mp-se/kegmon/raw/run1/screen.png

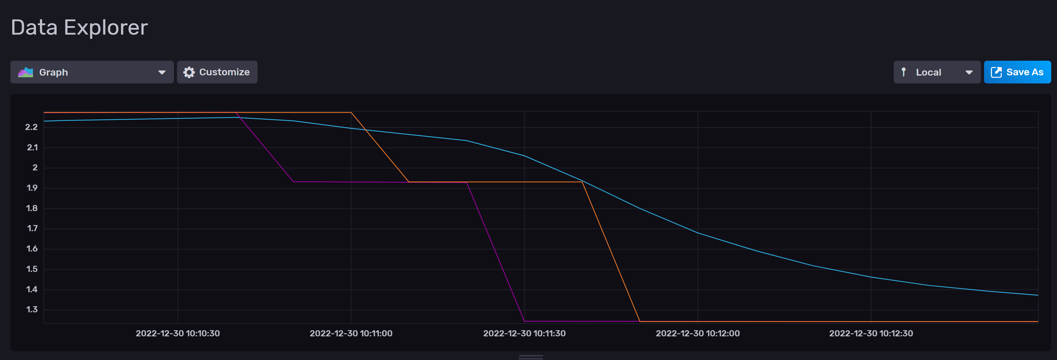
raw/run1/screen.png
