mp-se/kegmon/src_docs/source/images/view_other_about.png

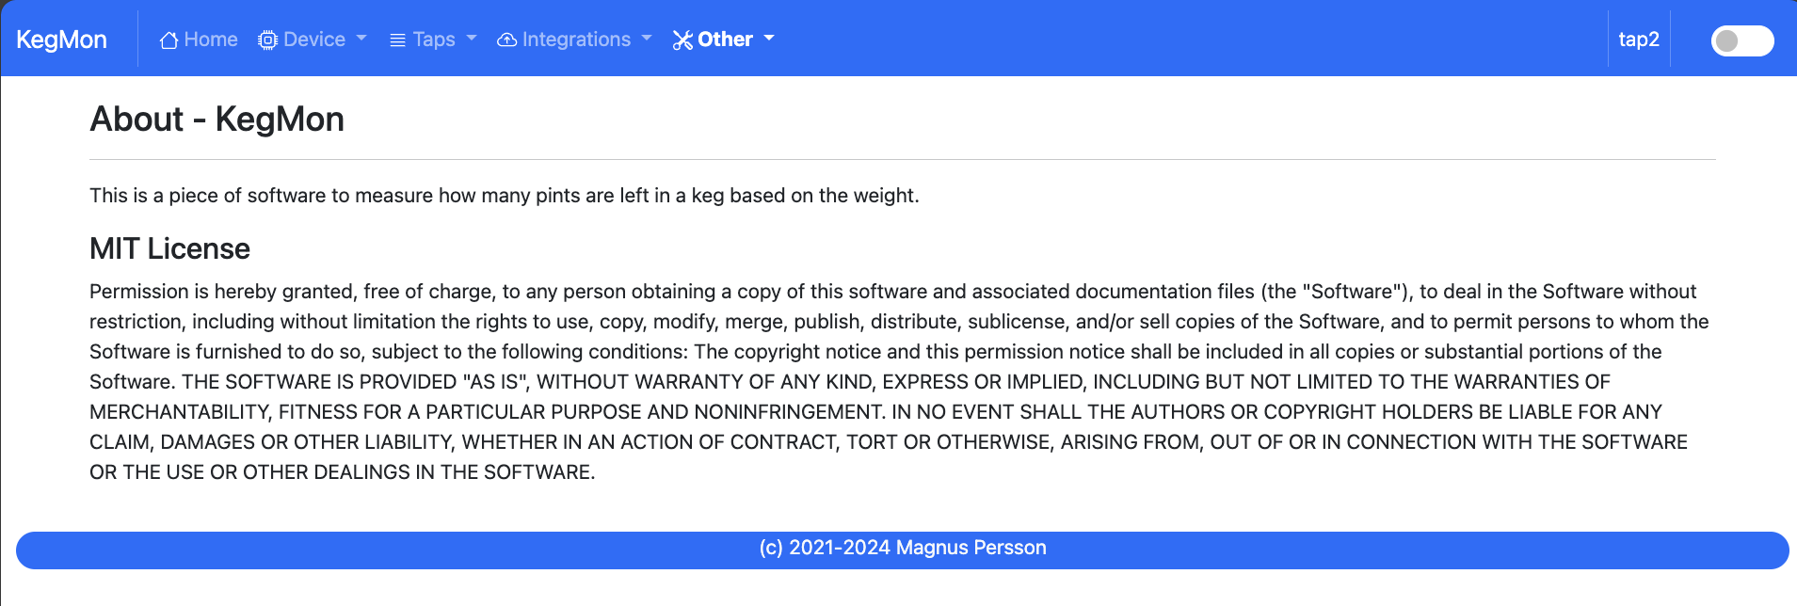
src_docs/source/images/view_other_about.png
