mp-se/kegmon/src/kegconfig.cpp

/*
MIT License

Copyright (c) 2021-2024 Magnus

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
THE SOFTWARE IS PROVIDED "AS IS", WITHOUT WARRANTY OF ANY KIND, EXPRESS OR
IMPLIED, INCLUDING BUT NOT LIMITED TO THE WARRANTIES OF MERCHANTABILITY,
FITNESS FOR A PARTICULAR PURPOSE AND NONINFRINGEMENT. IN NO EVENT SHALL THE
AUTHORS OR COPYRIGHT HOLDERS BE LIABLE FOR ANY CLAIM, DAMAGES OR OTHER
LIABILITY, WHETHER IN AN ACTION OF CONTRACT, TORT OR OTHERWISE, ARISING FROM,
OUT OF OR IN CONNECTION WITH THE SOFTWARE OR THE USE OR OTHER DEALINGS IN THE
SOFTWARE.
 */
#include <kegconfig.hpp>
#include <log.hpp>
#include <main.hpp>
#include <utils.hpp>

constexpr auto PARAM_PLATFORM = "platform";

KegConfig::KegConfig(String baseMDNS, String fileName)
    : BaseConfig(baseMDNS, fileName) {}

void KegConfig::createJson(JsonObject& doc) const {
  // Call base class functions
  createJsonBase(doc);
  createJsonWifi(doc);
  createJsonOta(doc);
  createJsonPush(doc);

  // Handle project specific config
  doc[PARAM_WEIGHT_UNIT] = getWeightUnit();
  doc[PARAM_VOLUME_UNIT] = getVolumeUnit();

  doc[PARAM_DISPLAY_LAYOUT] = getDisplayLayoutTypeAsInt();
  doc[PARAM_TEMP_SENSOR] = getTempSensorTypeAsInt();
  doc[PARAM_SCALE_SENSOR] = getScaleSensorTypeAsInt();
  doc[PARAM_DISPLAY_DRIVER] = getDisplayDriverTypeAsInt();
  // doc[PARAM_LEVEL_DETECTION] = getLevelDetectionAsInt();

  doc[PARAM_BREWFATHER_APIKEY] = getBrewfatherApiKey();
  doc[PARAM_BREWFATHER_USERKEY] = getBrewfatherUserKey();

  doc[PARAM_BREWPI_URL] = getBrewpiUrl();
  doc[PARAM_CHAMBERCTRL_URL] = getChamberCtrlUrl();

  doc[PARAM_BREWLOGGER_URL] = getBrewLoggerUrl();

  doc[PARAM_BREWSPY_TOKEN1] = getBrewspyToken(UnitIndex::U1);
  doc[PARAM_BREWSPY_TOKEN2] = getBrewspyToken(UnitIndex::U2);

  doc[PARAM_BARHELPER_APIKEY] = getBarhelperApiKey();
  doc[PARAM_BARHELPER_MONITOR1] = getBarhelperMonitor(UnitIndex::U1);
  doc[PARAM_BARHELPER_MONITOR2] = getBarhelperMonitor(UnitIndex::U2);

  doc[PARAM_SCALE_TEMP_FORMULA1] =
      getScaleTempCompensationFormula(UnitIndex::U1);
  doc[PARAM_SCALE_FACTOR1] =
      serialized(String(getScaleFactor(UnitIndex::U1), 5));
  doc[PARAM_SCALE_OFFSET1] = getScaleOffset(UnitIndex::U1);
  doc[PARAM_KEG_WEIGHT1] =
      serialized(String(convertOutgoingWeight(getKegWeight(UnitIndex::U1)),
                        getWeightPrecision()));
  doc[PARAM_KEG_VOLUME1] = serialized(String(
      getKegVolume(UnitIndex::U1),
      getWeightPrecision()));  // Dont convert this part (drop down in UI)
  doc[PARAM_GLASS_VOLUME1] = serialized(String(
      getGlassVolume(UnitIndex::U1),
      getWeightPrecision()));  // Dont convert this part (drop down in UI)
  doc[PARAM_BEER_NAME1] = getBeerName(UnitIndex::U1);
  doc[PARAM_BEER_ID1] = getBeerId(UnitIndex::U1);
  doc[PARAM_BEER_ABV1] = serialized(String(getBeerABV(UnitIndex::U1), 2));
  doc[PARAM_BEER_FG1] = serialized(String(getBeerFG(UnitIndex::U1), 2));
  doc[PARAM_BEER_EBC1] = getBeerEBC(UnitIndex::U1);
  doc[PARAM_BEER_IBU1] = getBeerIBU(UnitIndex::U1);

  doc[PARAM_SCALE_TEMP_FORMULA2] =
      getScaleTempCompensationFormula(UnitIndex::U2);
  doc[PARAM_SCALE_FACTOR2] =
      serialized(String(getScaleFactor(UnitIndex::U2), 5));
  doc[PARAM_SCALE_OFFSET2] = getScaleOffset(UnitIndex::U2);
  doc[PARAM_KEG_WEIGHT2] =
      serialized(String(convertOutgoingWeight(getKegWeight(UnitIndex::U2)),
                        getWeightPrecision()));
  doc[PARAM_KEG_VOLUME2] = serialized(String(
      getKegVolume(UnitIndex::U2),
      getWeightPrecision()));  // Dont convert this part (drop down in UI)
  doc[PARAM_GLASS_VOLUME2] =
      serialized(String(getGlassVolume(UnitIndex::U2),
                        2));  // Dont convert this part (drop down in UI)
  doc[PARAM_BEER_NAME2] = getBeerName(UnitIndex::U2);
  doc[PARAM_BEER_ID2] = getBeerId(UnitIndex::U2);
  doc[PARAM_BEER_ABV2] = serialized(String(getBeerABV(UnitIndex::U2), 2));
  doc[PARAM_BEER_FG2] = serialized(String(getBeerFG(UnitIndex::U2), 2));
  doc[PARAM_BEER_EBC2] = getBeerEBC(UnitIndex::U2);
  doc[PARAM_BEER_IBU2] = getBeerIBU(UnitIndex::U2);

  doc[PARAM_SCALE_DEVIATION_INCREASE] =
      serialized(String(getScaleDeviationIncreaseValue(), 2));
  doc[PARAM_SCALE_DEVIATION_DECREASE] =
      serialized(String(getScaleDeviationDecreaseValue(), 2));
  doc[PARAM_SCALE_DEVIATION_KALMAN] =
      serialized(String(getScaleKalmanDeviationValue(), 2));
  doc[PARAM_SCALE_READ_COUNT] = getScaleReadCount();
  doc[PARAM_SCALE_READ_COUNT_CALIBRATION] = getScaleReadCountCalibration();
  doc[PARAM_SCALE_STABLE_COUNT] = getScaleStableCount();

  doc[PARAM_PIN_DISPLAY_DATA] = getPinDisplayData();
  doc[PARAM_PIN_DISPLAY_CLOCK] = getPinDisplayClock();
  doc[PARAM_PIN_SCALE1_DATA] = getPinScale1Data();
  doc[PARAM_PIN_SCALE1_CLOCK] = getPinScale1Clock();
  doc[PARAM_PIN_SCALE2_DATA] = getPinScale2Data();
  doc[PARAM_PIN_SCALE2_CLOCK] = getPinScale2Clock();
  doc[PARAM_PIN_TEMP_DATA] = getPinTempData();
  doc[PARAM_PIN_TEMP_POWER] = getPinTempPower();

#if defined(ESP8266)
  doc[PARAM_PLATFORM] = "esp8266";
#elif defined(ESP32S2)
  doc[PARAM_PLATFORM] = "esp32s2";
#elif defined(ESP32S3)
  doc[PARAM_PLATFORM] = "esp32s3";
#else
#error "Unsupported target"
#endif

  /*
  doc[PARAM_KALMAN_ACTIVE] = isKalmanActive();
  doc[PARAM_KALMAN_MEASUREMENT] = getKalmanMeasurement();
  doc[PARAM_KALMAN_ESTIMATION] = getKalmanEstimation();
  doc[PARAM_KALMAN_NOISE] = getKalmanNoise();
  */
}

void KegConfig::parseJson(JsonObject& doc) {
  // Call base class functions
  parseJsonBase(doc);
  parseJsonWifi(doc);
  parseJsonOta(doc);
  parseJsonPush(doc);

  // Handle project specific config
  if (!doc[PARAM_WEIGHT_UNIT].isNull()) setWeightUnit(doc[PARAM_WEIGHT_UNIT]);
  if (!doc[PARAM_VOLUME_UNIT].isNull()) setVolumeUnit(doc[PARAM_VOLUME_UNIT]);

  if (!doc[PARAM_BREWFATHER_APIKEY].isNull())
    setBrewfatherApiKey(doc[PARAM_BREWFATHER_APIKEY]);
  if (!doc[PARAM_BREWFATHER_USERKEY].isNull())
    setBrewfatherUserKey(doc[PARAM_BREWFATHER_USERKEY]);

  if (!doc[PARAM_BREWPI_URL].isNull()) setBrewpiUrl(doc[PARAM_BREWPI_URL]);
  if (!doc[PARAM_CHAMBERCTRL_URL].isNull())
    setChamberCtrlUrl(doc[PARAM_CHAMBERCTRL_URL]);

  if (!doc[PARAM_BREWLOGGER_URL].isNull())
    setBrewLoggerUrl(doc[PARAM_BREWLOGGER_URL]);

  if (!doc[PARAM_BREWSPY_TOKEN1].isNull())
    setBrewspyToken(UnitIndex::U1, doc[PARAM_BREWSPY_TOKEN1]);
  if (!doc[PARAM_BREWSPY_TOKEN2].isNull())
    setBrewspyToken(UnitIndex::U2, doc[PARAM_BREWSPY_TOKEN2]);

  if (!doc[PARAM_BARHELPER_APIKEY].isNull())
    setBarhelperApiKey(doc[PARAM_BARHELPER_APIKEY]);

  if (!doc[PARAM_BARHELPER_MONITOR1].isNull())
    setBarhelperMonitor(UnitIndex::U1, doc[PARAM_BARHELPER_MONITOR1]);
  if (!doc[PARAM_BARHELPER_MONITOR2].isNull())
    setBarhelperMonitor(UnitIndex::U2, doc[PARAM_BARHELPER_MONITOR2]);

  if (!doc[PARAM_DISPLAY_LAYOUT].isNull())
    setDisplayLayoutType(doc[PARAM_DISPLAY_LAYOUT].as<int>());
  if (!doc[PARAM_TEMP_SENSOR].isNull())
    setTempSensorType(doc[PARAM_TEMP_SENSOR].as<int>());
  if (!doc[PARAM_SCALE_SENSOR].isNull())
    setScaleSensorType(doc[PARAM_SCALE_SENSOR].as<int>());
  if (!doc[PARAM_DISPLAY_DRIVER].isNull())
    setDisplayDriverType(doc[PARAM_DISPLAY_DRIVER].as<int>());

  /*if (!doc[PARAM_LEVEL_DETECTION].isNull())
    setLevelDetection(doc[PARAM_LEVEL_DETECTION].as<int>());*/

  if (!doc[PARAM_SCALE_TEMP_FORMULA1].isNull())
    setScaleTempCompensationFormula(UnitIndex::U1,
                                    doc[PARAM_SCALE_TEMP_FORMULA1]);
  if (!doc[PARAM_SCALE_FACTOR1].isNull())
    setScaleFactor(UnitIndex::U1, doc[PARAM_SCALE_FACTOR1].as<float>());
  if (!doc[PARAM_SCALE_OFFSET1].isNull())
    setScaleOffset(UnitIndex::U1, doc[PARAM_SCALE_OFFSET1].as<float>());
  if (!doc[PARAM_KEG_WEIGHT1].isNull())
    setKegWeight(UnitIndex::U1,
                 convertIncomingWeight(doc[PARAM_KEG_WEIGHT1].as<float>()));
  if (!doc[PARAM_KEG_VOLUME1].isNull())
    setKegVolume(
        UnitIndex::U1,
        doc[PARAM_KEG_VOLUME1]
            .as<float>());  // No need to convert this, always in Liters
  if (!doc[PARAM_GLASS_VOLUME1].isNull())
    setGlassVolume(
        UnitIndex::U1,
        doc[PARAM_GLASS_VOLUME1]
            .as<float>());  // No need to convert this, always in Liters
  if (!doc[PARAM_BEER_NAME1].isNull())
    setBeerName(UnitIndex::U1, doc[PARAM_BEER_NAME1]);
  if (!doc[PARAM_BEER_ID1].isNull())
    setBeerId(UnitIndex::U1, doc[PARAM_BEER_ID1]);
  if (!doc[PARAM_BEER_EBC1].isNull())
    setBeerEBC(UnitIndex::U1, doc[PARAM_BEER_EBC1].as<int>());
  if (!doc[PARAM_BEER_ABV1].isNull())
    setBeerABV(UnitIndex::U1, doc[PARAM_BEER_ABV1].as<float>());
  if (!doc[PARAM_BEER_IBU1].isNull())
    setBeerIBU(UnitIndex::U1, doc[PARAM_BEER_IBU1].as<int>());
  if (!doc[PARAM_BEER_FG1].isNull())
    setBeerFG(UnitIndex::U1, doc[PARAM_BEER_FG1].as<float>());

  if (!doc[PARAM_SCALE_TEMP_FORMULA2].isNull())
    setScaleTempCompensationFormula(UnitIndex::U2,
                                    doc[PARAM_SCALE_TEMP_FORMULA2]);
  if (!doc[PARAM_SCALE_FACTOR2].isNull())
    setScaleFactor(UnitIndex::U2, doc[PARAM_SCALE_FACTOR2].as<float>());
  if (!doc[PARAM_SCALE_OFFSET2].isNull())
    setScaleOffset(UnitIndex::U2, doc[PARAM_SCALE_OFFSET2].as<float>());
  if (!doc[PARAM_KEG_WEIGHT2].isNull())
    setKegWeight(UnitIndex::U2,
                 convertIncomingWeight(doc[PARAM_KEG_WEIGHT2].as<float>()));
  if (!doc[PARAM_KEG_VOLUME2].isNull())
    setKegVolume(
        UnitIndex::U2,
        doc[PARAM_KEG_VOLUME2]
            .as<float>());  // No need to convert this, always in Liters
  if (!doc[PARAM_GLASS_VOLUME2].isNull())
    setGlassVolume(
        UnitIndex::U2,
        doc[PARAM_GLASS_VOLUME2]
            .as<float>());  // No need to convert this, always in Liters
  if (!doc[PARAM_BEER_NAME2].isNull())
    setBeerName(UnitIndex::U2, doc[PARAM_BEER_NAME2]);
  if (!doc[PARAM_BEER_ID2].isNull())
    setBeerId(UnitIndex::U2, doc[PARAM_BEER_ID2]);
  if (!doc[PARAM_BEER_EBC2].isNull())
    setBeerEBC(UnitIndex::U2, doc[PARAM_BEER_EBC2].as<int>());
  if (!doc[PARAM_BEER_ABV2].isNull())
    setBeerABV(UnitIndex::U2, doc[PARAM_BEER_ABV2].as<float>());
  if (!doc[PARAM_BEER_IBU2].isNull())
    setBeerIBU(UnitIndex::U2, doc[PARAM_BEER_IBU2].as<int>());
  if (!doc[PARAM_BEER_FG2].isNull())
    setBeerFG(UnitIndex::U2, doc[PARAM_BEER_FG2].as<float>());

  if (!doc[PARAM_SCALE_DEVIATION_DECREASE].isNull())
    setScaleDeviationDecreaseValue(doc[PARAM_SCALE_DEVIATION_DECREASE]);
  if (!doc[PARAM_SCALE_DEVIATION_INCREASE].isNull())
    setScaleDeviationIncreaseValue(doc[PARAM_SCALE_DEVIATION_INCREASE]);
  if (!doc[PARAM_SCALE_DEVIATION_KALMAN].isNull())
    setScaleKalmanDeviationValue(doc[PARAM_SCALE_DEVIATION_KALMAN]);
  if (!doc[PARAM_SCALE_READ_COUNT].isNull())
    setScaleReadCount(doc[PARAM_SCALE_READ_COUNT]);
  if (!doc[PARAM_SCALE_READ_COUNT_CALIBRATION].isNull())
    setScaleReadCountCalibration(doc[PARAM_SCALE_READ_COUNT_CALIBRATION]);
  if (!doc[PARAM_SCALE_STABLE_COUNT].isNull())
    setScaleStableCount(doc[PARAM_SCALE_STABLE_COUNT]);

  if (!doc[PARAM_PIN_DISPLAY_DATA].isNull())
    setPinDisplayData(doc[PARAM_PIN_DISPLAY_DATA]);
  if (!doc[PARAM_PIN_DISPLAY_CLOCK].isNull())
    setPinDisplayClock(doc[PARAM_PIN_DISPLAY_CLOCK]);
  if (!doc[PARAM_PIN_SCALE1_DATA].isNull())
    setPinScale1Data(doc[PARAM_PIN_SCALE1_DATA]);
  if (!doc[PARAM_PIN_SCALE1_CLOCK].isNull())
    setPinScale1Clock(doc[PARAM_PIN_SCALE1_CLOCK]);
  if (!doc[PARAM_PIN_SCALE2_DATA].isNull())
    setPinScale2Data(doc[PARAM_PIN_SCALE2_DATA]);
  if (!doc[PARAM_PIN_SCALE2_CLOCK].isNull())
    setPinScale2Clock(doc[PARAM_PIN_SCALE2_CLOCK]);
  if (!doc[PARAM_PIN_TEMP_DATA].isNull())
    setPinTempData(doc[PARAM_PIN_TEMP_DATA]);
  if (!doc[PARAM_PIN_TEMP_POWER].isNull())
    setPinTempPower(doc[PARAM_PIN_TEMP_POWER]);

  /*
  if (!doc[PARAM_KALMAN_ESTIMATION].isNull())
    setKalmanEstimation(doc[PARAM_KALMAN_ESTIMATION].as<float>());
  if (!doc[PARAM_KALMAN_MEASUREMENT].isNull())
    setKalmanMeasurement(doc[PARAM_KALMAN_MEASUREMENT].as<float>());
  if (!doc[PARAM_KALMAN_NOISE].isNull())
    setKalmanNoise(doc[PARAM_KALMAN_NOISE].as<float>());
  if (!doc[PARAM_KALMAN_ACTIVE].isNull()) {
    String s = doc[PARAM_KALMAN_ACTIVE];
    setKalmanActive(s.equals("yes") ? true : false);
  }*/
}

float convertIncomingWeight(float w) {
  float r;

  if (myConfig.isWeightUnitKG())
    r = w;
  else
    r = convertLBStoKG(w);

#if LOG_LEVEL == 6
  // Log.verbose(F("CFG : Convering %F to %F (%s)." CR), w, r,
  // myConfig.getWeightUnit());
#endif
  return r;
}

float convertIncomingVolume(float v) {
  float r;

  if (myConfig.isVolumeUnitCL())
    r = v * 100.0;
  else if (myConfig.isVolumeUnitUSOZ())
    r = convertUSOZtoCL(v);
  else
    r = convertUKOZtoCL(v);

#if LOG_LEVEL == 6
  // Log.verbose(F("CFG : Converting incoming volume %F to %F (%s)." CR), v,
  // r, myConfig.getVolumeUnit());
#endif
  return r;
}

float convertOutgoingWeight(float w) {
  float r;

  if (myConfig.isWeightUnitKG())
    r = w;
  else
    r = convertKGtoLBS(w);

#if LOG_LEVEL == 6
  // Log.verbose(F("CFG : Converting outgoing weight %F to %F (%s)." CR), w,
  // r, myConfig.getWeightUnit());
#endif
  return r;
}

float convertOutgoingVolume(float v) {
  float r;

  if (myConfig.isVolumeUnitCL())
    r = (v == 0.0 ? 0.0 : v * 100.0);
  else if (myConfig.isVolumeUnitUSOZ())
    r = convertCLtoUSOZ(v == 0.0 ? 0.0 : v * 100.0);
  else
    r = convertCLtoUKOZ(v == 0.0 ? 0.0 : v * 100.0);

#if LOG_LEVEL == 6
  // Log.verbose(F("CFG : Converting outgoing volume %F to %F (%s)." CR), v,
  // r, myConfig.getVolumeUnit());
#endif
  return r;
}

float convertOutgoingTemperature(float t) {
  if (myConfig.isTempFormatC()) return t;
  return convertCtoF(t);
}

void KegConfig::migrateSettings() {
  constexpr auto CFG_FILENAME_OLD = "/kegmon.json";
  constexpr auto CFG_FILENAME_OLD_SAVE = "/kegmon_old.json";

  if (!LittleFS.exists(CFG_FILENAME_OLD)) {
    return;
  }

  File configFile = LittleFS.open(CFG_FILENAME_OLD, "r");

  if (!configFile) {
    Serial.println("Failed to open old config file");
    return;
  }

  JsonDocument doc;
  JsonDocument doc2;

  DeserializationError err = deserializeJson(doc, configFile);
  configFile.close();

  if (err) {
    Serial.println("Failed to open parse old config file");
    return;
  }

  JsonObject obj = doc.to<JsonObject>();
  JsonObject obj2 = doc2.to<JsonObject>();

  serializeJson(obj, EspSerial);
  EspSerial.print(CR);

  for (JsonPair kv : obj) {
    String k = kv.key().c_str();
    k.replace("-", "_");
    obj2[k] = obj[kv.key().c_str()];
  }

  obj.clear();
#if LOG_LEVEL == 6
  serializeJson(obj2, EspSerial);
  EspSerial.print(CR);
#endif
  parseJson(obj2);
  obj2.clear();

  if (saveFile()) {
    LittleFS.rename(CFG_FILENAME_OLD, CFG_FILENAME_OLD_SAVE);
    // LittleFS.remove(CFG_FILENAME_OLD);
  }

  Log.notice(F("CFG : Migrated old config /kegmon.json." CR));
}

// EOF
