mp-se/kegmon/src/config.hpp

/*
MIT License

Copyright (c) 2021-22 Magnus

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
THE SOFTWARE IS PROVIDED "AS IS", WITHOUT WARRANTY OF ANY KIND, EXPRESS OR
IMPLIED, INCLUDING BUT NOT LIMITED TO THE WARRANTIES OF MERCHANTABILITY,
FITNESS FOR A PARTICULAR PURPOSE AND NONINFRINGEMENT. IN NO EVENT SHALL THE
AUTHORS OR COPYRIGHT HOLDERS BE LIABLE FOR ANY CLAIM, DAMAGES OR OTHER
LIABILITY, WHETHER IN AN ACTION OF CONTRACT, TORT OR OTHERWISE, ARISING FROM,
OUT OF OR IN CONNECTION WITH THE SOFTWARE OR THE USE OR OTHER DEALINGS IN THE
SOFTWARE.
 */
#ifndef SRC_CONFIG_HPP_
#define SRC_CONFIG_HPP_

#include <main.hpp>

#define CFG_APPNAME "KegScale"         // Name of firmware
#define CFG_FILENAME "/kegscale.json"  // Name of config file

struct BeerInfo {
  String _name = "";
  float _abv = 0.0;
  int _ebc = 0;
  int _ibu = 0;
};

class Config {
 private:
  bool _saveNeeded = false;

  String _id = "";
  String _mDNS = "";
  char _tempFormat = 'C';
  int _weightPrecision = 2;
  String _wifiSSID[2] = {"", ""};
  String _wifiPASS[2] = {"", ""};
  String _brewfatherUserKey = "";
  String _brewfatherApiKey = "";

  float _scaleFactor[2] = {0, 0};
  int32_t _scaleOffset[2] = {0, 0};
  float _kegWeight[2] = {0, 0};
  float _pintWeight[2] = {0, 0};
  BeerInfo _beer[2];

  void formatFileSystem();

 public:
  Config();
  const char* getID() { return _id.c_str(); }
  int getWifiConnectionTimeout() { return 30; }
  int getWifiPortalTimeout() { return 120; }

  const char* getBrewfatherUserKey() { return _brewfatherUserKey.c_str(); }
  void setBrewfatherUserKey(String s) {
    _brewfatherUserKey = s;
    _saveNeeded = true;
  }
  const char* getBrewfatherApiKey() { return _brewfatherApiKey.c_str(); }
  void setBrewfatherApiKey(String s) {
    _brewfatherApiKey = s;
    _saveNeeded = true;
  }

  const char* getBeerName(int idx) { return _beer[idx]._name.c_str(); }
  void setBeerName(int idx, String s) {
    _beer[idx]._name = s;
    _saveNeeded = true;
  }
  float getBeerABV(int idx) { return _beer[idx]._abv; }
  void setBeerABV(int idx, float f) {
    _beer[idx]._abv = f;
    _saveNeeded = true;
  }
  int getBeerEBC(int idx) { return _beer[idx]._ebc; }
  void setBeerEBC(int idx, int i) {
    _beer[idx]._ebc = i;
    _saveNeeded = true;
  }
  int getBeerIBU(int idx) { return _beer[idx]._ibu; }
  void setBeerIBU(int idx, int i) {
    _beer[idx]._ibu = i;
    _saveNeeded = true;
  }

  float getKegWeight(int idx) { return _kegWeight[idx]; }
  void setKegWeight(int idx, float f) {
    _kegWeight[idx] = f;
    _saveNeeded = true;
  }

  float getPintWeight(int idx) { return _pintWeight[idx]; }
  void setPintWeight(int idx, float f) {
    _pintWeight[idx] = f;
    _saveNeeded = true;
  }

  int getWeightPrecision() { return _weightPrecision; }
  void setWeightPrecision(int i) {
    _weightPrecision = i;
    _saveNeeded = true;
  }

  int32_t getScaleOffset(int idx) { return _scaleOffset[idx]; }
  void setScaleOffset(int idx, int32_t l) {
    _scaleOffset[idx] = l;
    _saveNeeded = true;
  }

  float getScaleFactor(int idx) { return _scaleFactor[idx]; }
  void setScaleFactor(int idx, float f) {
    _scaleFactor[idx] = f;
    _saveNeeded = true;
  }

  const char* getMDNS() { return _mDNS.c_str(); }
  void setMDNS(String s) {
    _mDNS = s;
    _saveNeeded = true;
  }

  const char* getWifiSSID(int idx) { return _wifiSSID[idx].c_str(); }
  void setWifiSSID(String s, int idx) {
    _wifiSSID[idx] = s;
    _saveNeeded = true;
  }
  const char* getWifiPass(int idx) { return _wifiPASS[idx].c_str(); }
  void setWifiPass(String s, int idx) {
    _wifiPASS[idx] = s;
    _saveNeeded = true;
  }

  char getTempFormat() { return _tempFormat; }
  void setTempFormat(char c) {
    if (c == 'C' || c == 'F') {
      _tempFormat = c;
      _saveNeeded = true;
    }
  }
  bool isTempC() { return _tempFormat == 'C'; }
  bool isTempF() { return _tempFormat == 'F'; }

  void createJson(DynamicJsonDocument& doc);
  bool saveFile();
  bool loadFile();
  void checkFileSystem();
  bool isSaveNeeded() { return _saveNeeded; }
  void setSaveNeeded() { _saveNeeded = true; }
};

extern Config myConfig;

#endif  // SRC_CONFIG_HPP_

// EOF
