mp-se/kegmon/src/levels.hpp

/*
MIT License

Copyright (c) 2021-2024 Magnus

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
THE SOFTWARE IS PROVIDED "AS IS", WITHOUT WARRANTY OF ANY KIND, EXPRESS OR
IMPLIED, INCLUDING BUT NOT LIMITED TO THE WARRANTIES OF MERCHANTABILITY,
FITNESS FOR A PARTICULAR PURPOSE AND NONINFRINGEMENT. IN NO EVENT SHALL THE
AUTHORS OR COPYRIGHT HOLDERS BE LIABLE FOR ANY CLAIM, DAMAGES OR OTHER
LIABILITY, WHETHER IN AN ACTION OF CONTRACT, TORT OR OTHERWISE, ARISING FROM,
OUT OF OR IN CONNECTION WITH THE SOFTWARE OR THE USE OR OTHER DEALINGS IN THE
SOFTWARE.
 */
#ifndef SRC_LEVELS_HPP_
#define SRC_LEVELS_HPP_

#include <Arduino.h>

#include <kegconfig.hpp>
#include <levelraw.hpp>
#include <levelstatistic.hpp>
#include <stability.hpp>
#include <weightvolume.hpp>

constexpr auto LEVELS_FILEMAXSIZE = 2000;

class LevelDetection {
 private:
  Stability _stability[2];
  RawLevelDetection* _rawLevel[2] = {0, 0};
  StatsLevelDetection* _statsLevel[2] = {0, 0};

  LevelDetection(const LevelDetection&) = delete;
  void operator=(const LevelDetection&) = delete;

  void logLevels(float kegVolume1, float kegVolume2, float pourVolume1,
                 float pourVolume2);
  void pushKegUpdate(UnitIndex idx, float stableVol, float pourVol,
                     float glasses);
  void pushPourUpdate(UnitIndex idx, float stableVol, float pourVol);

 public:
  LevelDetection();
  void update(UnitIndex idx, float raw, float temp);

  Stability* getStability(UnitIndex idx) { return &_stability[idx]; }
  RawLevelDetection* getRawDetection(UnitIndex idx) { return _rawLevel[idx]; }
  StatsLevelDetection* getStatsDetection(UnitIndex idx) {
    return _statsLevel[idx];
  }

  // Return values based on the chosen algoritm
  bool hasStableWeight(UnitIndex idx,
                       LevelDetectionType type = myConfig.getLevelDetection());
  bool hasPourWeight(UnitIndex idx,
                     LevelDetectionType type = myConfig.getLevelDetection());

  float getBeerWeight(UnitIndex idx,
                      LevelDetectionType type = myConfig.getLevelDetection());
  float getBeerStableWeight(
      UnitIndex idx, LevelDetectionType type = myConfig.getLevelDetection());
  float getPourWeight(UnitIndex idx,
                      LevelDetectionType type = myConfig.getLevelDetection());

  float getTotalWeight(UnitIndex idx,
                       LevelDetectionType type = myConfig.getLevelDetection());
  float getTotalStableWeight(
      UnitIndex idx, LevelDetectionType type = myConfig.getLevelDetection());

  // Return the raw data (last value from scale)
  float getTotalRawWeight(UnitIndex idx);

  // Returns weights in liters
  float getBeerVolume(UnitIndex idx,
                      LevelDetectionType type = myConfig.getLevelDetection()) {
    WeightVolumeConverter conv(idx);
    return conv.weightToVolume(getBeerWeight(idx, type));
  }

  float getBeerStableVolume(
      UnitIndex idx, LevelDetectionType type = myConfig.getLevelDetection()) {
    WeightVolumeConverter conv(idx);
    return conv.weightToVolume(getBeerStableWeight(idx, type));
  }

  float getPourVolume(UnitIndex idx,
                      LevelDetectionType type = myConfig.getLevelDetection()) {
    WeightVolumeConverter conv(idx);
    return conv.weightToVolume(getPourWeight(idx, type));
  }

  float getNoGlasses(UnitIndex idx,
                     LevelDetectionType type = myConfig.getLevelDetection()) {
    WeightVolumeConverter conv(idx);
    return conv.weightToGlasses(getBeerWeight(idx, type));
  }

  float getNoStableGlasses(
      UnitIndex idx, LevelDetectionType type = myConfig.getLevelDetection()) {
    WeightVolumeConverter conv(idx);
    return conv.weightToGlasses(getBeerStableWeight(idx, type));
  }
};

extern LevelDetection myLevelDetection;

#endif  // SRC_LEVELS_HPP_

// EOF
